rmd6502/flappy/Arduino/hardware/flappy/cores/flappy/wiring.c

/*
  wiring.c - Partial implementation of the Wiring API for the ATmega8.
  Part of Arduino - http://www.arduino.cc/

  Copyright (c) 2005-2006 David A. Mellis

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
  $Id$
*/

#include "wiring_private.h"

// the prescaler is set so that timer1 ticks every 64 clock cycles, and the
// the overflow handler is called every 256 ticks.
#define MICROSECONDS_PER_TIMER1_OVERFLOW (clockCyclesToMicroseconds(8 * 65536))

// the whole number of milliseconds per timer1 overflow
#define MILLIS_INC (MICROSECONDS_PER_TIMER1_OVERFLOW / 1000)

// the fractional number of milliseconds per timer1 overflow. we shift right
// by three to fit these numbers into a byte. (for the clock speeds we care
// about - 8 and 16 MHz - this doesn't lose precision.)
#define FRACT_INC ((MICROSECONDS_PER_TIMER1_OVERFLOW % 1000) >> 3)
#define FRACT_MAX (1000 >> 3)

volatile unsigned long timer1_overflow_count = 0;
volatile unsigned long timer1_millis = 0;
static unsigned char timer1_fract = 0;

ISR(TIM1_OVF_vect)
{
	// copy these to local variables so they can be stored in registers
	// (volatile variables must be read from memory on every access)
	unsigned long m = timer1_millis;
	unsigned char f = timer1_fract;

	m += MILLIS_INC;
	f += FRACT_INC;
	if (f >= FRACT_MAX) {
		f -= FRACT_MAX;
		m += 1;
	}

	timer1_fract = f;
	timer1_millis = m;
	timer1_overflow_count++;
}

unsigned long millis()
{
	unsigned long m;
	uint8_t oldSREG = SREG;

	// disable interrupts while we read timer1_millis or we might get an
	// inconsistent value (e.g. in the middle of a write to timer1_millis)
	cli();
	m = timer1_millis;
	SREG = oldSREG;

	return m;
}

unsigned long micros() {
	unsigned long m;
	uint8_t oldSREG = SREG, t;
	
	cli();
	m = timer1_overflow_count;
#if defined(TCNT1)
	t = TCNT1;
#elif defined(TCNT1L)
	t = TCNT1L;
#else
	#error TIMER 1 not defined
#endif

  
#ifdef TIFR1
	if ((TIFR1 & _BV(TOV1)) && (t < 255))
		m++;
#else
	if ((TIFR & _BV(TOV1)) && (t < 255))
		m++;
#endif

	SREG = oldSREG;
	
	return ((m << 8) + t) * (8 / clockCyclesPerMicrosecond());
}

void delay(unsigned long ms)
{
	uint16_t start = (uint16_t)micros();

	while (ms > 0) {
		if (((uint16_t)micros() - start) >= 1000) {
			ms--;
			start += 1000;
		}
	}
}

/* Delay for the given number of microseconds.  Assumes a 8 or 16 MHz clock. */
void delayMicroseconds(unsigned int us)
{
	// calling avrlib's delay_us() function with low values (e.g. 1 or
	// 2 microseconds) gives delays longer than desired.
	//delay_us(us);
#if F_CPU >= 20000000L
	// for the 20 MHz clock on rare Arduino boards

	// for a one-microsecond delay, simply wait 2 cycle and return. The overhead
	// of the function call yields a delay of exactly a one microsecond.
	__asm__ __volatile__ (
		"nop" "\n\t"
		"nop"); //just waiting 2 cycle
	if (--us == 0)
		return;

	// the following loop takes a 1/5 of a microsecond (4 cycles)
	// per iteration, so execute it five times for each microsecond of
	// delay requested.
	us = (us<<2) + us; // x5 us

	// account for the time taken in the preceeding commands.
	us -= 2;

#elif F_CPU >= 16000000L
	// for the 16 MHz clock on most Arduino boards

	// for a one-microsecond delay, simply return.  the overhead
	// of the function call yields a delay of approximately 1 1/8 us.
	if (--us == 0)
		return;

	// the following loop takes a quarter of a microsecond (4 cycles)
	// per iteration, so execute it four times for each microsecond of
	// delay requested.
	us <<= 2;

	// account for the time taken in the preceeding commands.
	us -= 2;
#else
	// for the 8 MHz internal clock on the ATmega168

	// for a one- or two-microsecond delay, simply return.  the overhead of
	// the function calls takes more than two microseconds.  can't just
	// subtract two, since us is unsigned; we'd overflow.
	if (--us == 0)
		return;
	if (--us == 0)
		return;

	// the following loop takes half of a microsecond (4 cycles)
	// per iteration, so execute it twice for each microsecond of
	// delay requested.
	us <<= 1;
    
	// partially compensate for the time taken by the preceeding commands.
	// we can't subtract any more than this or we'd overflow w/ small delays.
	us--;
#endif

	// busy wait
	__asm__ __volatile__ (
		"1: sbiw %0,1" "\n\t" // 2 cycles
		"brne 1b" : "=w" (us) : "0" (us) // 2 cycles
	);
}

void init()
{
	
    cli();
    TCCR1A = 0;
    TCCR1B = _BV(CS11);
    TCNT1 = 0;
	// enable timer 1 overflow interrupt
#if defined(TIMSK) && defined(TOIE1)
	sbi(TIMSK, TOIE1);
#elif defined(TIMSK1) && defined(TOIE1)
	sbi(TIMSK1, TOIE1);
#else
	#error	Timer 1 overflow interrupt not set correctly
#endif
	// this needs to be called before setup() or some functions won't
	// work there
	sei();

#if defined(ADCSRA)
	// set a2d prescale factor to 128
	// 16 MHz / 128 = 125 KHz, inside the desired 50-200 KHz range.
	// XXX: this will not work properly for other clock speeds, and
	// this code should use F_CPU to determine the prescale factor.
	sbi(ADCSRA, ADPS2);
	sbi(ADCSRA, ADPS1);
	sbi(ADCSRA, ADPS0);

	// enable a2d conversions
	sbi(ADCSRA, ADEN);
#endif

	// the bootloader connects pins 0 and 1 to the USART; disconnect them
	// here so they can be used as normal digital i/o; they will be
	// reconnected in Serial.begin()
#if defined(UCSRB)
	UCSRB = 0;
#elif defined(UCSR0B)
	UCSR0B = 0;
#endif
}
